martinclausen2/RGBW-Lampe/Core/Src/setbrightness.c

/*
 * setbrightness.c
 *
 *  Created on: 24.12.2019
 *      Author: Martin
 */

#include "setbrightness.h"

TIM_HandleTypeDef *htim_PWM;					//handle to address timer

bool LightOn;
int FocusChannel;
unsigned char Brightness[maxVirtualChannel];		//current value

unsigned int PWM_Offset[maxChannel] = {0};	 		//PWM value, where the driver effectively starts to generate an output
unsigned char WriteTimer;							/* time until Brightness is saved in calls to StoreBrightness() */

signed int PWM_set[maxChannel] = {0};				//current PWM value
signed int PWM_incr[maxChannel] = {0};				//PWM dimming step size
unsigned int PWM_incr_cnt[maxChannel] = {0};		//no of steps required to reach target PWM value
unsigned int PWM_step_cnt[maxChannel] = {0};		//no of steps until next PWM step
unsigned int PWM_step_cnt_reload[maxChannel] = {0};	//no of steps required between two PWM steps, required to fade more smoothly for slow and small changes seen with wake up and mod light

void PWM_Init(TIM_HandleTypeDef *handle_tim)
{
	htim_PWM = handle_tim;
	htim_PWM->Instance->CCR1 = 0;
	htim_PWM->Instance->CCR2 = 0;
	htim_PWM->Instance->CCR3 = 0;
	htim_PWM->Instance->CCR4 = 0;
	HAL_TIM_PWM_Start(htim_PWM, TIM_CHANNEL_1);
	HAL_TIM_PWM_Start(htim_PWM, TIM_CHANNEL_2);
	HAL_TIM_PWM_Start(htim_PWM, TIM_CHANNEL_3);
	HAL_TIM_PWM_Start(htim_PWM, TIM_CHANNEL_4);
	for (int i = 0; i < maxChannel;	i++)
	{
		PWM_Offset[i]  = GLOBAL_settings_ptr->PWM_Offset[i];
		PWM_Offset[i] *= PWM_Offset[i];
	}
}

unsigned int PWM_SetPulseWidth(int channel)
{
	unsigned int temp;

	PWM_set[channel] += PWM_incr[channel];
	--PWM_incr_cnt[channel];
	//limit to 16 bit
	if (PWM_set[channel] > maxPWM)
	{
		PWM_set[channel] = maxPWM;
	}
	else if (PWM_set[channel] < 0)
	{
		PWM_set[channel] = 0;
	}
	temp = PWM_set[channel] + PWM_Offset[channel];
	if (temp > maxPWM)
	{
		temp = maxPWM;
	}
	else if (temp < 0)
	{
		temp = 0;
	}
	return temp;
}

void PWM_StepDim()		// perform next dimming step, must frequently called for dimming action
// contains repeated code to optimize performance
{
	if (PWM_incr_cnt[0])
	{
		if (PWM_step_cnt[0])
		{
			PWM_step_cnt[0]--;
		}
		else
		{
			htim_PWM->Instance->CCR3 = PWM_SetPulseWidth(0);
			PWM_step_cnt[0] = PWM_step_cnt_reload[0];
		}
	}

	if (PWM_incr_cnt[1])
	{
		if (PWM_step_cnt[1])
		{
			PWM_step_cnt[1]--;
		}
		else
		{
			htim_PWM->Instance->CCR1 = PWM_SetPulseWidth(1);

			PWM_step_cnt[1] = PWM_step_cnt_reload[1];
		}
	}

	if (PWM_incr_cnt[2])
	{
		if (PWM_step_cnt[2])
		{
			PWM_step_cnt[2]--;
		}
		else
		{
			htim_PWM->Instance->CCR4 = PWM_SetPulseWidth(2);
			PWM_step_cnt[2] = PWM_step_cnt_reload[2];}
	}

	if (PWM_incr_cnt[3])
	{
		if (PWM_step_cnt[3])
		{
			PWM_step_cnt[3]--;
		}
		else
		{
			htim_PWM->Instance->CCR2 = PWM_SetPulseWidth(3);
			PWM_step_cnt[3] = PWM_step_cnt_reload[3];}
	}
}

void PWM_SetupDim(unsigned char i, signed int PWM_dimsteps, signed int brightnessStep, unsigned int timeSteps)
{
	signed int temp;
	limit=0;						//reset limit indicator

	temp = Brightness[i] + brightnessStep;
	if (GLOBAL_settings_ptr->maxBrightness[i] < temp)		//avoid overflow
	{
		temp = GLOBAL_settings_ptr->maxBrightness[i];
		limit = maxLimit;
	}
	else if (0 > temp)
	{
		limit = minLimit;
		temp = 0;
	}
	Brightness[i] = temp;

	if (i < maxChannel)
	{
		PWM_step_cnt_reload[i] = timeSteps;
		PWM_step_cnt[i] = timeSteps;

		temp = temp * temp - PWM_set[i];
		if ((temp > PWM_dimsteps) || (-temp>PWM_dimsteps))		// if we have more difference then steps to go
		{
			PWM_incr[i] = temp / PWM_dimsteps;
			PWM_set[i] += (temp - PWM_incr[i]*PWM_dimsteps); 	//calculate remainder, brackets to avoid overflow!?
			PWM_incr_cnt[i] = PWM_dimsteps;
		}
		else
		{
			if (0<temp)		// if we would have a step size smaller then one, we better reduce the number of steps
			{
				PWM_incr[i] = 1;
				PWM_incr_cnt[i] = temp;
			}
			else if (0>temp)
			{
				PWM_incr[i] = -1;
				PWM_incr_cnt[i] = -temp;				//count must be a positive number!
			}
		}
	}
}

void PWM_SetupNow(unsigned char i, signed char Steps)
{
	PWM_SetupDim(i, 1, Steps, 0);
	PWM_StepDim();
}

unsigned int sqrt32(unsigned long a)
{
	unsigned int rem=0;
	unsigned int root=0;
	unsigned int divisor=0;
	int i;

	// Iterate 16 times, because the maximum number of bits in the result is 16 bits
	for(i=0;i<16;i++)
	{
		root<<=1;
		rem=(rem << 2)+(a>>30);
		a<<=2;
		divisor=(root<<1)+1;
		if (divisor<=rem)
		{
			rem-=divisor;
			root+=1;
		}
	}
	return root;
}

void SwLightOn(unsigned char i, unsigned int relBrightness)
{
	unsigned long temp;
	unsigned char minBrightness;					//avoid reduction to very low brightness values by external light
	unsigned char maxBrightness;
	unsigned char startBrightness;

	minBrightness = GLOBAL_settings_ptr->minBrightness[i];
	maxBrightness = GLOBAL_settings_ptr->maxBrightness[i];
	startBrightness = GLOBAL_settings_ptr->Brightness_start[i];
	temp=(startBrightness*relBrightness)>>4;
	if (maxBrightness < temp)						//limit brightness to maximum
	{
		Brightness[i] = maxBrightness;
	}
	else if ((startBrightness>temp) && (minBrightness>temp))		//limit brightness ..
	{
		if (minBrightness>startBrightness)
		{
			Brightness[i] = startBrightness;		// .. to last value if it is smaller than minimum brightness
		}
		else
		{
			Brightness[i] = minBrightness;			// .. to minimum brightness if the last value was larger than the minimum brightness
		}
	}
	else
	{
		Brightness[i] = temp;						// or just take the calculated value!
	}
	PWM_SetupDim(i, fadetime, 0, 0);
}

void SwLightOff(unsigned char i)
{
	GLOBAL_settings_ptr->Brightness_start[i]=Brightness[i];
	Brightness[i]=0;
	PWM_SetupDim(i, fadetime, 0, 0);
}

void SwAllLightOn()
{
	unsigned int relBrightness;
	if (LightOn == false)						//remote signal might try to switch a switched on light on again
	{
		FocusChannel=startupfocus;
		LightOn=true;
		unsigned int ExtBrightness_last = GLOBAL_settings_ptr->ExtBrightness_last;
		if (0==ExtBrightness_last)
		{
			ExtBrightness_last=1;
		}
		relBrightness=sqrt32(extBrightness/ExtBrightness_last);
		for (int i = 0; i < maxChannel;	i++)
		{
			SwLightOn(i, relBrightness);
		}
		LEDOn();
	}
}

void SwAllLightOff()
{
	if (LightOn == true)						//remote signal might try to switch a switched on light on again
	{
		LightOn=false;
		for (int i = 0; i < maxChannel;	i++)
		{
			SwLightOff(i);
		}
		HAL_Delay(750);
		SetExtBrightness_last();
		SenderMode=GLOBAL_settings_ptr->SenderMode; 		//reset mode
		LEDSetupStandby();
	}
}

void ToggleFocus()
{
	FocusChannel++;
	if (FocusChannel >= maxVirtualChannel)
		FocusChannel = 0;
}

int PreviewToggelFocus()
{
	int temp = FocusChannel;
	temp++;
	if (temp >= maxVirtualChannel)
		temp = 0;
	return temp;
}

void SetExtBrightness_last()
{
	unsigned int ExtBrightness_last=(extBrightness>>8) & 0xFFFF;
	GLOBAL_settings_ptr->ExtBrightness_last=ExtBrightness_last;
}

void StoreBrightness()
{
	if (1<WriteTimer)		/* store current brightness after timeout */
	{
		--WriteTimer;
	}
	else if (1 == WriteTimer)
	{
		if (LightOn)
		{
			memcpy(GLOBAL_settings_ptr->Brightness_start, Brightness, sizeof(Brightness));
			SetExtBrightness_last();
			SettingsWrite();
		}
		WriteTimer=0;
	}
}
