martinclausen2/RGBW-Lampe/Core/Inc/RC5.h

/*
 * RC5.h
 *
 *  Created on: Apr 05, 2021
 *      Author: Martin
 */

#ifndef RC5_H_
#define RC5_H_

#include "stm32l1xx_hal.h"
#include "setbrightness.h"
#include "settings.h"
#include "main.h"
#include <stdbool.h>
#include <stdio.h>

#define pulsesActive 32
#define pulsesInactive 32

#define maxComMode 3

#define ComModeOff	0
#define ComModeAlarm	1
#define ComModeConditional	2
#define ComModeAll	3

#define RC5Addr_first		27	//address for first light brightness
#define RC5Addr_com			29	//address for RC5 communication
#define maxRC5Address		31	//maximum possible RC5 address

#define RC5Cmd_AlarmStart	53	//code for start of alarm
#define RC5Cmd_AlarmEnd		54	//code for end of alarm
#define RC5Cmd_Off			13	//code for light off
#define RC5Cmd_On			12	//code for light on

#define RC5Cmd_Repeats		3	//number of repeats for on, off and AlarmStart commands
#define RC5Value_Repeats	1	//number of repeats for value transmission

#define RemoteSteps			2	//Step size for brightness control via remote control

extern unsigned char SenderMode;		//Mode for sending commands to other devices

//State Machine zur Decodierung des RC5-Fernbedienungscodes
static const unsigned char tblRemote[] =	{
		1, 0, 2, 0, 3, 0, 4, 0, 5, 0, 6, 0, 7, 0,
		8, 0, 9, 0, 10, 0, 11, 0, 12, 0, 13, 0, 14,
		0, 15, 0, 16, 0, 17, 0, 18, 0, 19, 0, 20, 0,
		20, 21, 0, 22, 0, 23, 26, 24, 26, 25, 26, 0,
		27, 0, 28, 0, 29, 31, 30, 31, 0, 31, 0, 32,
		0, 33, 35, 34, 35, 43, 36, 43, 37, 0, 38, 40,
		39, 40, 0, 40, 0, 41, 0, 42, 35, 34, 35, 44,
		0, 45, 48, 46, 48, 47, 48, 0, 49, 0, 50, 0, 34, 43};

void RC5_Init(TIM_HandleTypeDef *handle_tim_decode, TIM_HandleTypeDef *handle_tim_encode);
void RC5_decode(TIM_HandleTypeDef *htim);
void RC5_encode(TIM_HandleTypeDef *htim);
void RC5SignalSampling(GPIO_PinState signal);
void SetLightRemote(unsigned char i, signed char steps);
void SetBrightnessRemote(unsigned char i);
void SetBrightnessLevelRemote();
void DecodeRemote();
void SendRC5(unsigned char address, unsigned char code, unsigned char requiredmode, unsigned repeats);
void SendCommand(unsigned char address, unsigned char code, bool toggle);
void SendBit0();
void SendBit1();

#endif /* RC5_H_ */
