martinclausen2/RGBW-Lampe/Core/Src/wakeuplight.c

/*
 * wakeuplight.c
 *
 *  Created on: 14.04.2023
 *      Author: Martin
 */

#include "wakeuplight.h"

unsigned int AlarmDim_Cnt[maxChannel] = {0};
unsigned int AlarmDim_Cnt_Reload[maxChannel] = {0};

//stays on as long as the light fades in
bool AlarmFlag = false;

unsigned int Minutes2Signal = 0;
unsigned int Minutes2TimeOut = 0;

void CheckAlarm()
{
	if (alarmState.alarmTrigger)
	{
		alarmState.alarmTrigger = false;
		CLI_Printf("\r\nAlarm!");
		Rtc_GetDateTime();
		CLI_Printf("\r\nTimestamp: %02d-%02d-%02d %s %02d:%02d:%02d",
				dateRtc.Date, dateRtc.Month, dateRtc.Date, WeekdayNames[dateRtc.WeekDay],
				timeRtc.Hours, timeRtc.Minutes, timeRtc.Seconds);
		//load next alarm
		Rtc_SetAlarm();

		//execute a new alarm, but only if none is already running
		if (alarmState.skipAlarmCnt > 0)
			{
			CLI_Printf("\r\nAlarm skipped.");
			alarmState.skipAlarmCnt--;
			}
		else if (!AlarmFlag)
		{
			for (int i = 0; i < maxChannel;	i++)
			{
				// fade in to required brightness in on or off,
				// no fade in if already brighter, Alarm_StepDim() takes care of this behavior
				AlarmDim_Cnt_Reload[i]=(GLOBAL_settings_ptr->LightFading*callsinminute)/GLOBAL_settings_ptr->AlarmBrightness[i];
				AlarmDim_Cnt[i]=AlarmDim_Cnt_Reload[i];
			}
			LightOn=1;
			AlarmFlag=1;
			Minutes2Signal=GetTime2Singal();
			SendRC5(RC5Addr_com, RC5Cmd_AlarmStart, ComModeAlarm, RC5Cmd_Repeats);
		}
	}

	//wake-up light dimming all channels
	if (AlarmFlag)
	{
		for (int i = 0; i < maxChannel;	i++)
		{
			Alarm_StepDim(i);
		}

		//count down to start acoustic signal
		if (1 < Minutes2Signal)
		{
			--Minutes2Signal;
		}
		else if (1 == Minutes2Signal)
		{
			StartAcousticDDSAlarm();
			Minutes2TimeOut = alarmtimeout*callsinminute;
			Minutes2Signal = 0;
		}

		//count down to increase volume and finally to stop signal
		if (1 < Minutes2TimeOut)
		{
			--Minutes2TimeOut;
		}
		else if (1 == Minutes2TimeOut)
		{
			AlarmEnd();
			Minutes2TimeOut = 0;
		}

		if ((alarmtimeout*callsinminute/2) == Minutes2TimeOut)
		{
			SetVolumeAcousticDDSAlarm(GPIO_PIN_SET);
		}
	}
}

//stop any brightness increase, count down to acoustic alarm, or acoustic alarm
void AlarmEnd()
{
	if (AlarmFlag)
	{
		SendRC5(RC5Addr_com, RC5Cmd_AlarmEnd, ComModeAlarm, RC5Cmd_Repeats);
		AlarmFlag=0;
		Minutes2Signal = 0;
		Minutes2TimeOut = 0;
		StopAcousticDDSAlarm();
		LEDOn();
	}
}

void AlarmSnooze()
{
	if (AcousticAlarmFlag)
	{
		Minutes2Signal=callsinminute*((unsigned int)GLOBAL_settings_ptr->AlarmTimeSnooze);
		StopAcousticDDSAlarm();
	}
}

//wake-up light dimming
void Alarm_StepDim(unsigned char i)
{
	if (AlarmDim_Cnt[i])
	{
		--AlarmDim_Cnt[i];				//count down step
	}
	else								//dimming step
	{
		if (Brightness[i] < GLOBAL_settings_ptr->AlarmBrightness[i])
		{
			int dimsteps = Brightness[i] + AlarmBrightnessStep;
			dimsteps = dimsteps * dimsteps - Brightness[i] * Brightness[i];

			AlarmDim_Cnt[i]=AlarmDim_Cnt_Reload[i];		//reload count down
			PWM_SetupDim(i, dimsteps, AlarmBrightnessStep, AlarmDim_Cnt_Reload[i]*cases/dimsteps);	//setup brightness
		}
		else
		{
			AlarmFlag=0;				//we reached target brightness!
		}
	}
}


unsigned int GetTime2Singal()
{
	return callsinminute*((unsigned int)GLOBAL_settings_ptr->AlarmTime2Signal);
}
