martinclausen2/RGBW-Lampe/WLAN/device3.h

#define NTPserver "fritz.box"
#define MQTTbroker "192.168.178.123"
#define nodename "RGBW-Lampe3"
#define publishtopicstatus "RGBW-Lampe/3/status"
#define publishtopicNTP "RGBW-Lampe/3/NTP"
#define publishtopicswitch "RGBW-Lampe/3/switch"
#define subscribetopicswitch "RGBW-Lampe/switch"
#define subscribetopic "RGBW-Lampe"
