martinclausen2/RGBW-Lampe/Core/Src/sinetable.c

/*
 * sinetable.c
 *
 *  Created on: May 13, 2023
 *      Author: Martin
 */

#include "acousticddsalarm.h"

static const uint16_t __attribute__((unused)) sinetable [dacCacheSize] =
{
32513	,
33314	,
34114	,
34914	,
35712	,
36508	,
37302	,
38092	,
38880	,
39664	,
40443	,
41217	,
41986	,
42750	,
43507	,
44257	,
45001	,
45737	,
46464	,
47184	,
47894	,
48595	,
49286	,
49967	,
50638	,
51297	,
51945	,
52582	,
53206	,
53817	,
54416	,
55001	,
55573	,
56131	,
56674	,
57203	,
57716	,
58215	,
58697	,
59164	,
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
};
