martinclausen2/RGBW-Lampe/Core/Inc/keys.h

/*
 * keys.h
 *
 *  Created on: Dec 22, 2019
 *      Author: Martin
 */

#ifndef KEYS_H_
#define KEYS_H_

extern volatile unsigned char KeyState;			//stores the keys state
extern volatile unsigned char OldKeyState;
extern volatile unsigned char KeyPressDuration;

void Keys(unsigned int KeyState);
unsigned char CheckKeyPressed();

#endif /* KEYS_H_ */
